JustEcly/PancakeXXL-keyboard/img/pancakexxl_proto4-3.jpg

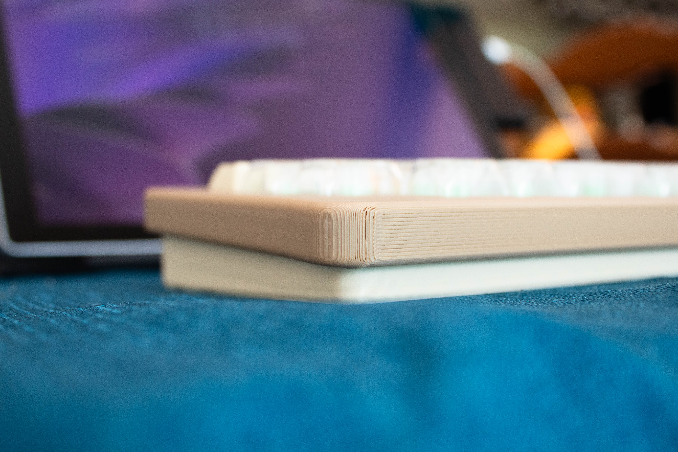
img/pancakexxl_proto4-3.jpg
