JustEcly/PancakeXXL-keyboard/img/pancakexxl_proto4-4.jpg

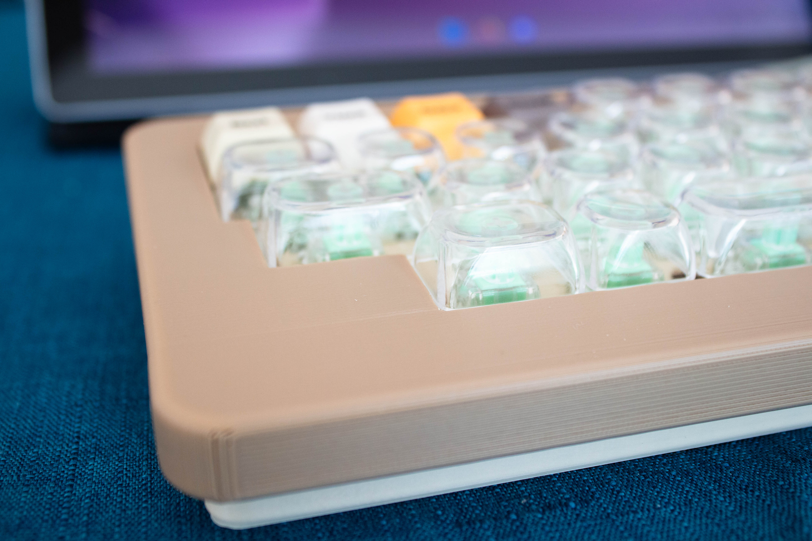
img/pancakexxl_proto4-4.jpg
