JustEcly/PancakeXXL-keyboard/plate_and_case/img/Back bottom-case.png

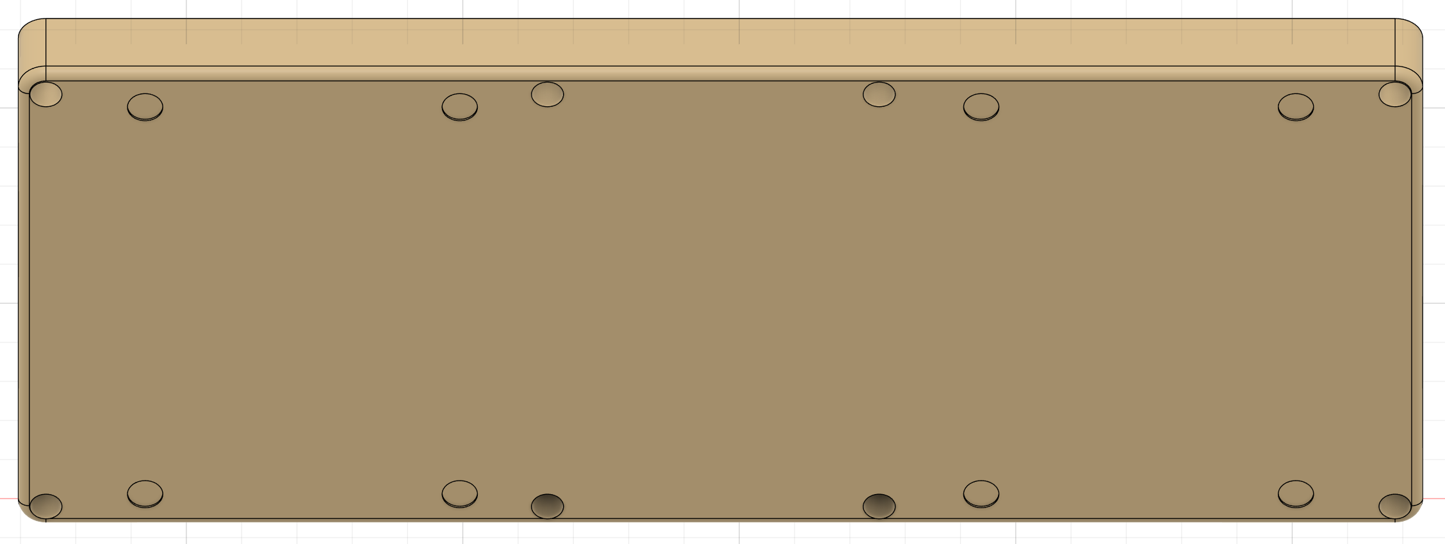
plate_and_case/img/Back bottom-case.png
