JustEcly/PancakeXXL-keyboard/plate_and_case/img/front bottom-case + UDB + plate.png

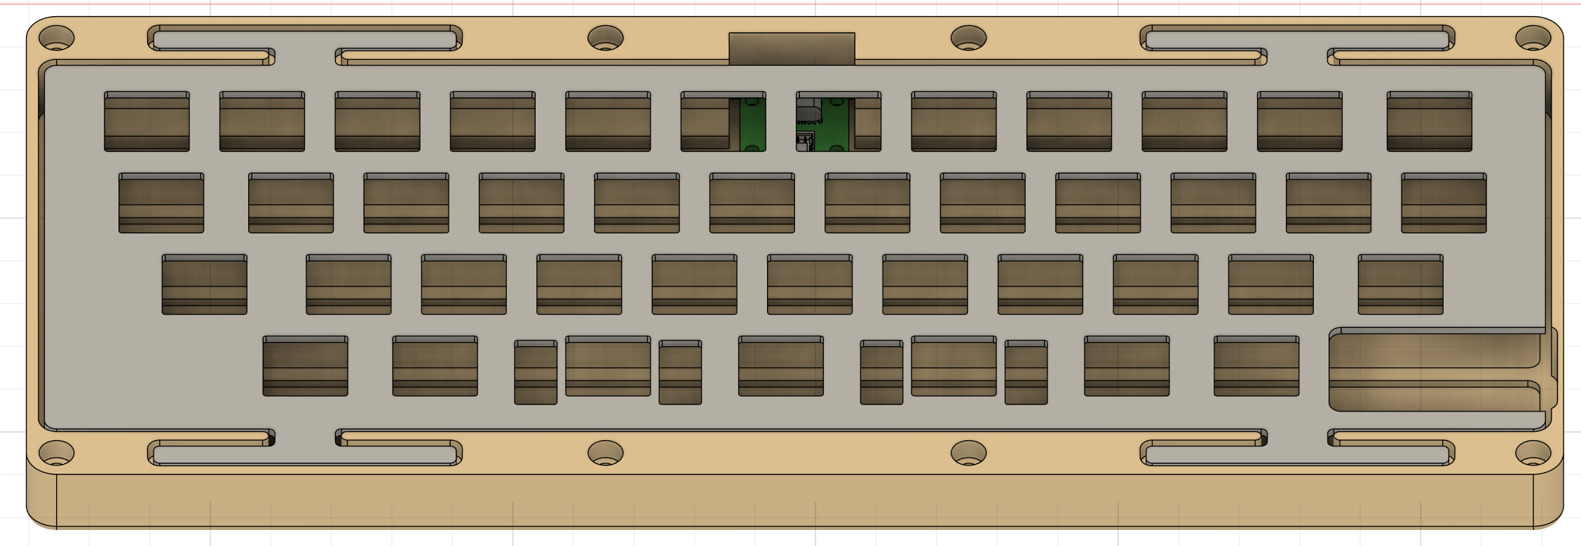
plate_and_case/img/front bottom-case + UDB + plate.png
