JustEcly/PancakeXXL-keyboard/plate_and_case/img/front bottom-case.png

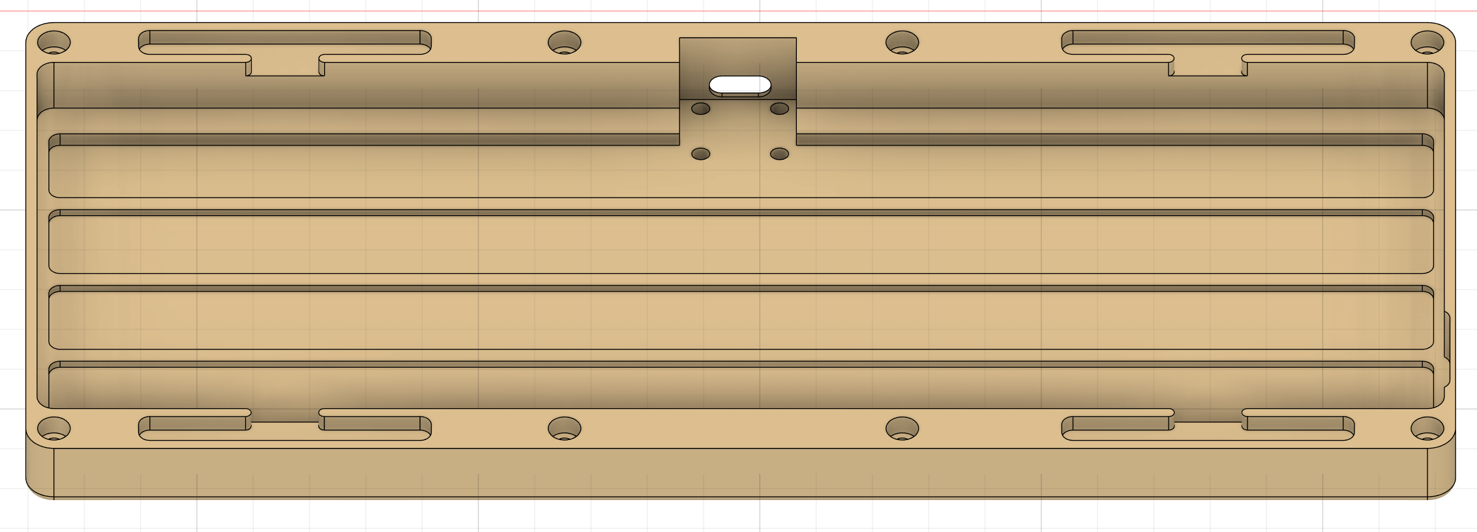
plate_and_case/img/front bottom-case.png
