JustEcly/PancakeXXL-keyboard/plate_and_case/img/front pcb + plate.png

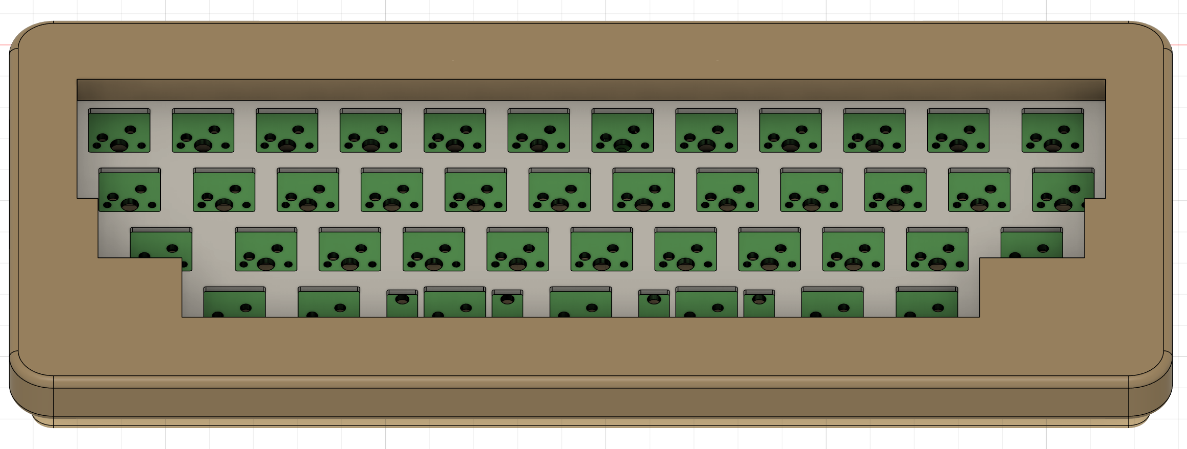
plate_and_case/img/front pcb + plate.png
