JustEcly/PancakeXXL-keyboard/plate_and_case/img/front plate + switch.png

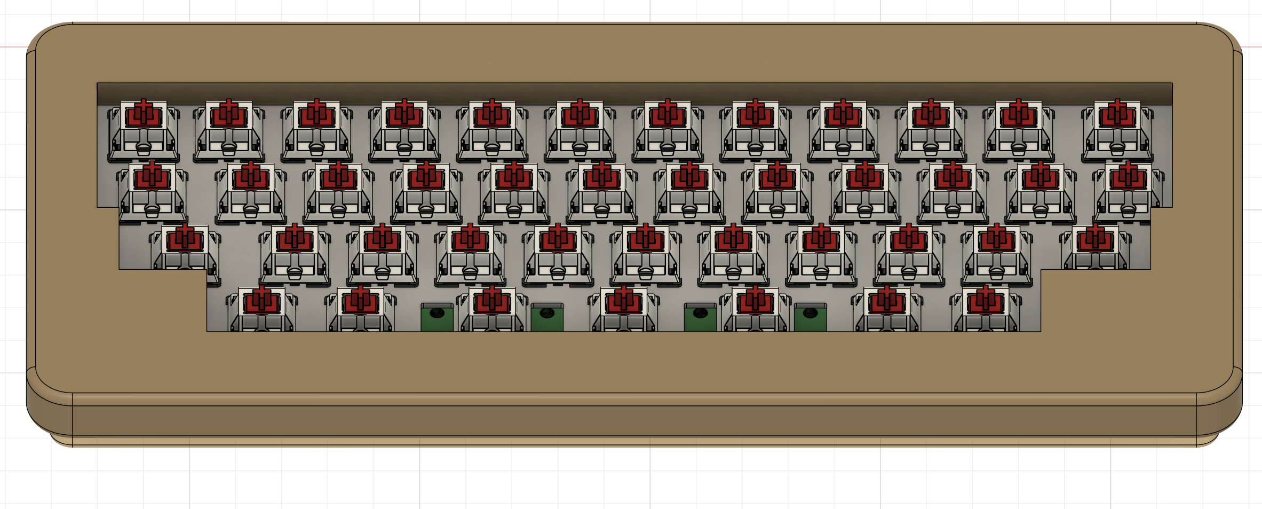
plate_and_case/img/front plate + switch.png
