JustEcly/PancakeXXL-keyboard/plate_and_case/img/Plate 2x2u.png

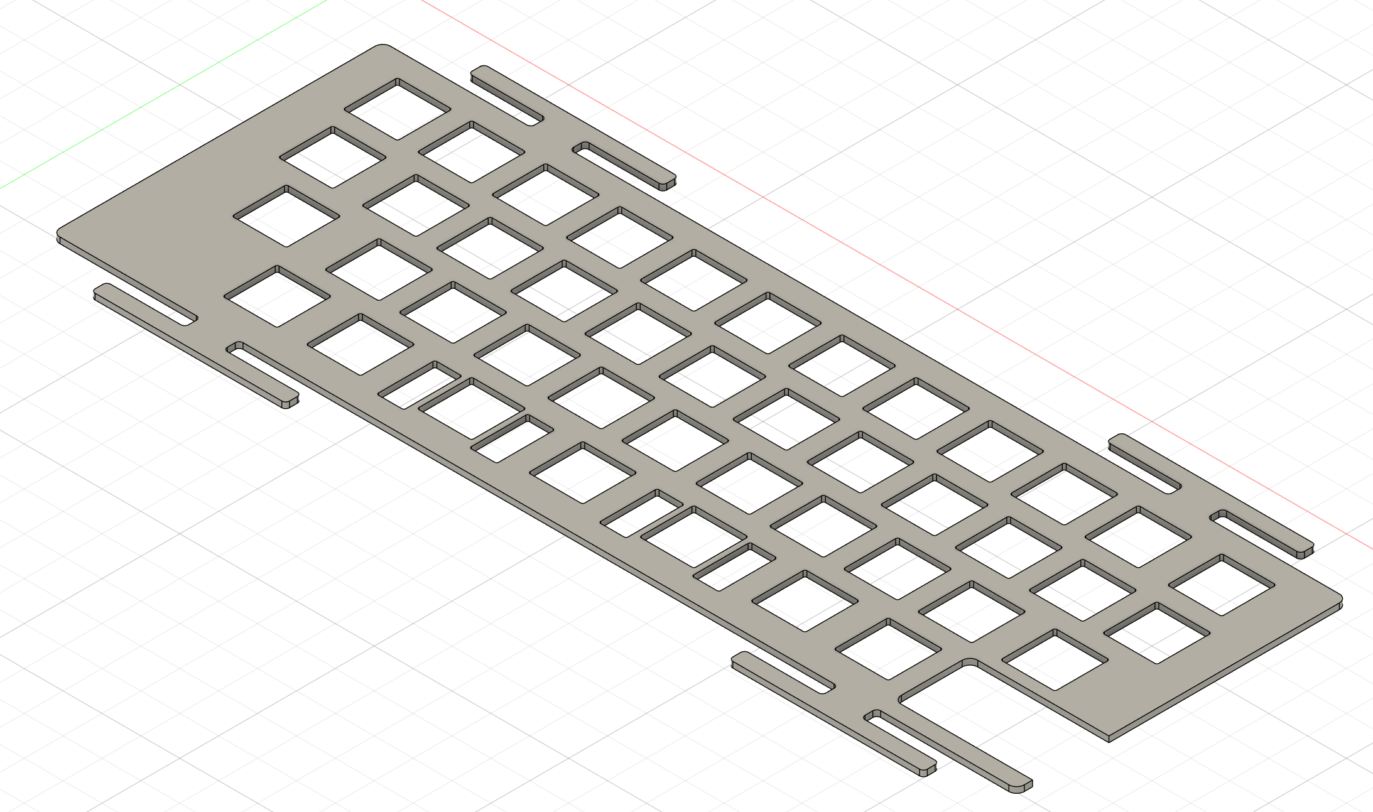
plate_and_case/img/Plate 2x2u.png
