JustEcly/PancakeXXL-keyboard/plate_and_case/img/Usb.png

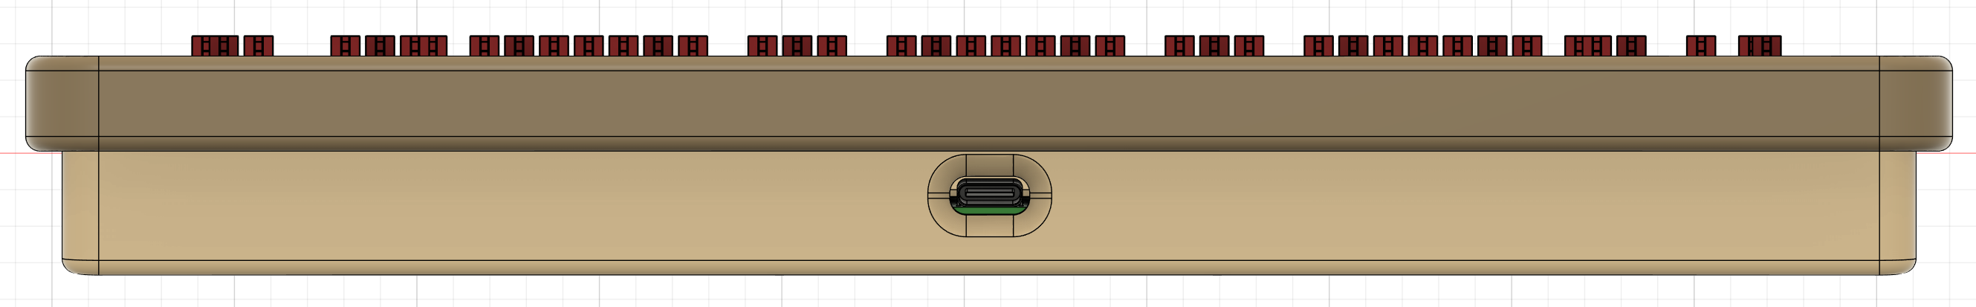
plate_and_case/img/Usb.png
